pablogs9/casa_cactus_speaker/cspot-ng/include/ShannonTCPClient.hpp

#pragma once

#include <interfaces/TCPClient.hpp>

#include <ByteArray.hpp>
#include <ByteUtils.hpp>
#include <Shannon.h>

namespace cspot_ng
{
    class ShannonTCPClient
    {
    public:
        ShannonTCPClient(TCPClient& tcp_client)
            : tcp_client_(tcp_client)
            , send_nonce_(0)
            , recv_nonce_(0)
        {
        }

        struct ShannonPacket
        {
            uint8_t command;
            ByteArray data;

            ByteArray get_raw() const
            {
                uint16_t total_size = sizeof(uint8_t) + sizeof(uint16_t) + data.size();

                ByteArray packet(total_size);
                packet[0] = command;

                packet[1] = (data.size() >> 8) & 0xFF;
                packet[2] = data.size() & 0xFF;
                std::memcpy(packet.data() + 3, data.data(), data.size());

                return packet;
            }
        };

        void send(const ShannonPacket& packet)
        {
            std::cout << "Send packet, command: " << static_cast<int>(packet.command) << std::endl;

            // Create a copy of the data that we can encrypt
            ByteArray encrypted_data = packet.get_raw();

            // Shannon encrypt the packet
            send_cipher_.encrypt(encrypted_data);

            // Generate MAC
            ByteArray mac(4); // MAC_SIZE is 4 bytes
            send_cipher_.finish(mac);

            // Update the nonce
            send_nonce_ += 1;
            auto nonce_vec = uint32_to_vector(htonl(send_nonce_));
            send_cipher_.nonce(nonce_vec);

            // Generate the complete message
            auto complete_msg = ByteArray();
            complete_msg.reserve(encrypted_data.size() + mac.size());
            complete_msg.insert(complete_msg.end(), encrypted_data.begin(), encrypted_data.end());
            complete_msg.insert(complete_msg.end(), mac.begin(), mac.end());
            tcp_client_.send(complete_msg);
        }

        ShannonPacket receive()
        {
            // Receive the initial 3 bytes (command + size)
            ByteArray header = tcp_client_.receive(3);

            if(header.size() == 0)
            {
                // Timeout
                return ShannonPacket();
            }

            if (header.size() < 3)
            {
                // Handle error (could throw exception or return an empty packet)
                std::cerr << "Failed to receive header" << std::endl;
                return ShannonPacket();
            }

            // Decrypt the header
            recv_cipher_.decrypt(header);

            // Extract command and size
            uint16_t size;
            memcpy(&size, header.data() + 1, sizeof(uint16_t));
            size = ntohs(size);
            uint8_t command = header[0];

            ShannonPacket packet;
            packet.command = command;

            if(size > 0)
            {
                packet.data = tcp_client_.receive(size);

                // Decrypt the data
                recv_cipher_.decrypt(packet.data);

                if (packet.data.size() != size)
                {
                    // Handle error (could throw exception or return an empty packet)
                    std::cerr << "Failed to receive complete data for command: " << static_cast<int>(command) << " expected size: " << size << " received size: " << packet.data.size() << std::endl;
                    return ShannonPacket();
                }
            }

            // Receive the MAC
            ByteArray mac = tcp_client_.receive(4);

            if (mac.size() < 4)
            {
                // Handle error (could throw exception or return an empty packet)
                std::cerr << "Failed to receive MAC" << std::endl;
                return ShannonPacket();
            }

            // Generate MAC for verification
            ByteArray calculated_mac(4); // MAC_SIZE is 4 bytes
            recv_cipher_.finish(calculated_mac);

            // Verify MAC (in production code, should handle mismatch)
            if (mac != calculated_mac)
            {
                std::cerr << "MAC mismatch on packet with command: " << static_cast<int>(command) <<  " and size: " << size << std::endl;
                // Handle MAC mismatch (could throw exception or log)
                return ShannonPacket();
            }

            // Update the nonce
            recv_nonce_ += 1;
            auto nonce_vec = uint32_to_vector(htonl(recv_nonce_));
            recv_cipher_.nonce(nonce_vec);

            // Return the decrypted data
            return packet;
        }

        void wrap_connection(const ByteArray& send_key, const ByteArray& recv_key)
        {
            // Set keys
            send_cipher_.key(send_key);
            recv_cipher_.key(recv_key);

            // Set initial nonces
            auto initial_nonce = uint32_to_vector(htonl(0));
            send_cipher_.nonce(initial_nonce);
            recv_cipher_.nonce(initial_nonce);

            // Reset nonce counters
            send_nonce_ = 0;
            recv_nonce_ = 0;

            // Mark as initialized
            initialized_ = true;
        }

        bool is_initialized() const
        {
            return initialized_;
        }

    private:
        TCPClient& tcp_client_;
        Shannon send_cipher_;
        Shannon recv_cipher_;

        uint32_t send_nonce_;
        uint32_t recv_nonce_;

        bool initialized_ = false;

        ByteArray uint32_to_vector(uint32_t value)
        {
            ByteArray result(4);
            result[3] = (value >> 24) & 0xFF;
            result[2] = (value >> 16) & 0xFF;
            result[1] = (value >> 8) & 0xFF;
            result[0] = value & 0xFF;
            return result;
        }
    };
};
